ericklein/air_quality/data.h

#ifndef DATA_H
#define DATA_H

// Define tag keys used to store important device attributes in
// InfluxDB.  Will be used as InfluxDB tag keys for the associated
// attribute.  Only relevant to InfluxDB (not MQTT).  Maps directly
// to the important data tag values set in config.h, which are
// expected to be customized there on a per installation basis.  These,
// however, should not be changed.
#define TAG_KEY_DEVICE     "device"     // Maps to DEVICE in config.h
#define TAG_KEY_DEVICE_ID  "device_id"  // Maps to DEVICE_ID in config.h
#define TAG_KEY_SITE       "site"       // Maps to SITE in config.h
#define TAG_KEY_LOCATION   "location"   // Maps to LOCATION in config.h
#define TAG_KEY_ROOM       "room"       // Maps to ROOM in config.h

// Defines value keys (strings) used for representing stored 
// sensor and device data as key/value pairs in InfluxDB and
// as parts of MQTT topics.  Must be unique, and must conform
// to syntax required for field keys by InfluxDB and MQTT.

#define VALUE_KEY_TEMPERATURE   "tempF"
#define VALUE_KEY_HUMIDITY      "humidity"
#define VALUE_KEY_CO2           "co2"
// #define VALUE_KEY_PRESSURE      "pressure"
// #define VALUE_KEY_PM25          "pm25"
// #define VALUE_KEY_AQI           "aqi"
#define VALUE_KEY_BATTERY_VOLTS "battery_volts"
// #define VALUE_KEY_BATTERY_PCT   "battery_pct"
#define VALUE_KEY_RSSI          "rssi"
// #define VALUE_KEY_NETWORK_IP    "network_ip"
// #define VALUE_KEY_VERSION       "version"

#endif  // #ifdef DATA_H
