ericklein/air_quality/secrets_template.h

/*
  Project:		air_quality
  Description:	private configuration data template that needs to be saved as secrets.h after github cloning the project
*/

// Configuration Step 1: Set site environment variables
// set the site altitude in meters to calibrate the SCD40
// Example; downtown Pasadena, CA (SuperCon!) is at 236m
// #define SITE_ALTITUDE	236

// Configuration Step 2: Set WiFi credentials
// #ifdef WIFI
// 	#define WIFI_SSID	"key_value"
// 	#define WIFI_PASS   "key_value"
// #endif

// Configuration Step 3: Set Open Weather Map credential and location
//	#define OWM_KEY 		"keyvalue"
// 	#define OWM_LAT_LONG	"lat=34.1448&lon=-118.1509" // Pasadena, CA

// Configuration Step 4: If using MQTT, set MQTT broker login parameters
// #ifdef MQTT
// 	#define MQTT_PORT  		port_number	// use 8883 for SSL
// 	#define MQTT_USER		"key_value"
// 	#define MQTT_BROKER		"ip_address"
// 	#define MQTT_PASS 		"key_value"
// #endif

// Configuration Step 5: If using influxdb, set login and storage parameters
// #ifdef INFLUX
	// For an InfluxDB v1.X server:
	// #define INFLUX_V1
	// #define INFLUXDB_URL 
	// #define INFLUXDB_DB_NAME
	// #define INFLUXDB_USER
	// #define INFLUXDB_PASSWORD

	// For an InfluxDB v2.X server:
	// #define INFLUX_V2 
	// #define INFLUXDB_URL "http://ip_address:port_number"
	// #define INFLUXDB_TOKEN "key_value"
	// #define INFLUXDB_ORG "key_value"
	// #define INFLUXDB_BUCKET "key_value"
// #endif

// Configuration Step 6: Set key device and installation configuration parameters.  These are used
// widely throughout the code to properly identify the device and generate important
// operating elements like MQTT topics, InfluxDB data tags (metadata).  Should be
// customized to match the target installation. Values here are examples.
// #define DEVICE           "key_value"	// e.g. name of device, "realtime_co2"
// #define DEVICE_SITE      "key_value"	// e.g. physical address of the device, "1234 Main Street"
// #define DEVICE_LOCATION  "key_value"	// e.g. general location of device at physical address, "indoor"
// #define DEVICE_ROOM      "key_value"	// e.g. specific location of device within location, "kitchen"
// #define DEVICE_ID        "key_value"	// e.g. unique ID for the device, "007"
